BrianWalczak/BKFZ-SubGHz/Other/Mockups/1.png

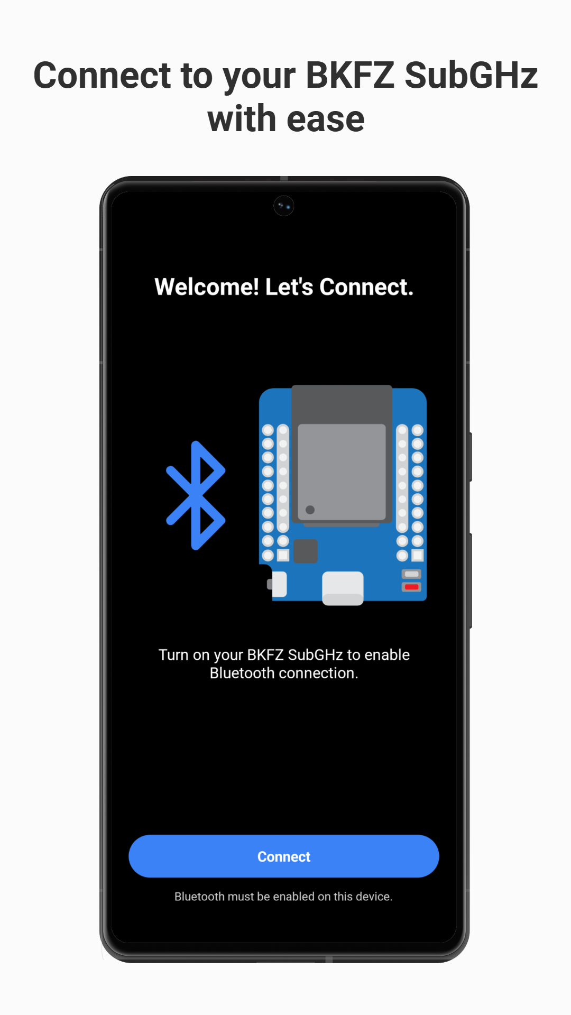
Other/Mockups/1.png
