BrianWalczak/BKFZ-SubGHz/Other/Mockups/2.png

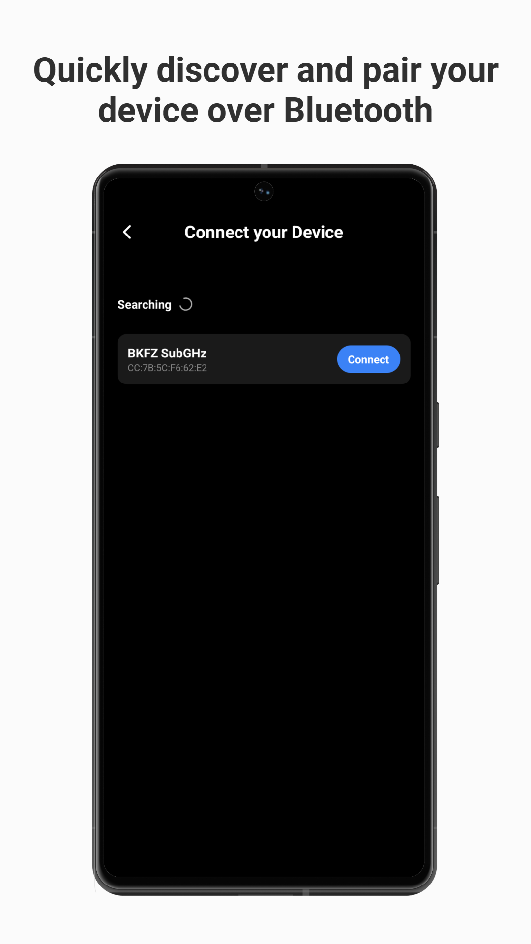
Other/Mockups/2.png
