BrianWalczak/BKFZ-SubGHz/Other/Mockups/3.png

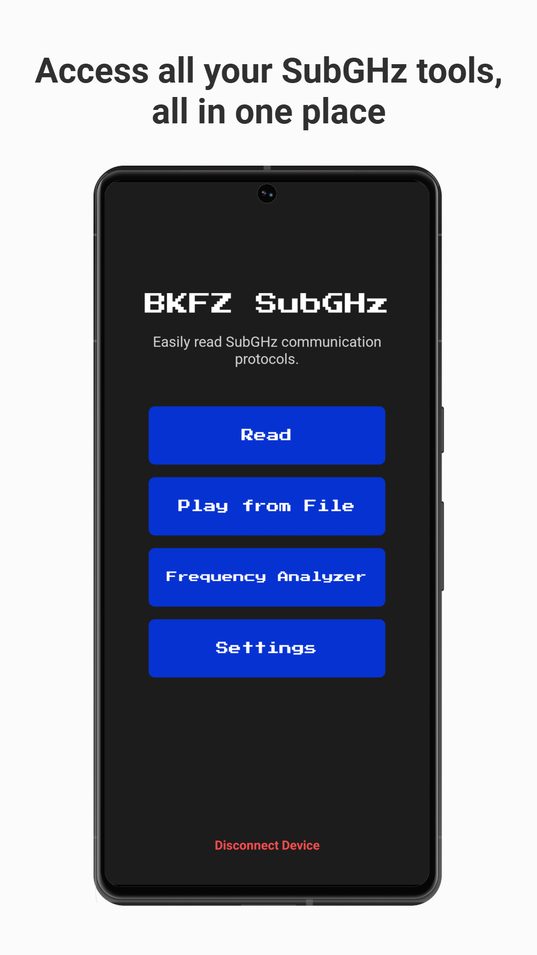
Other/Mockups/3.png
