BrianWalczak/BKFZ-SubGHz/Other/Assembly Photos/Step 1. Soldering to PCB (after).jpeg

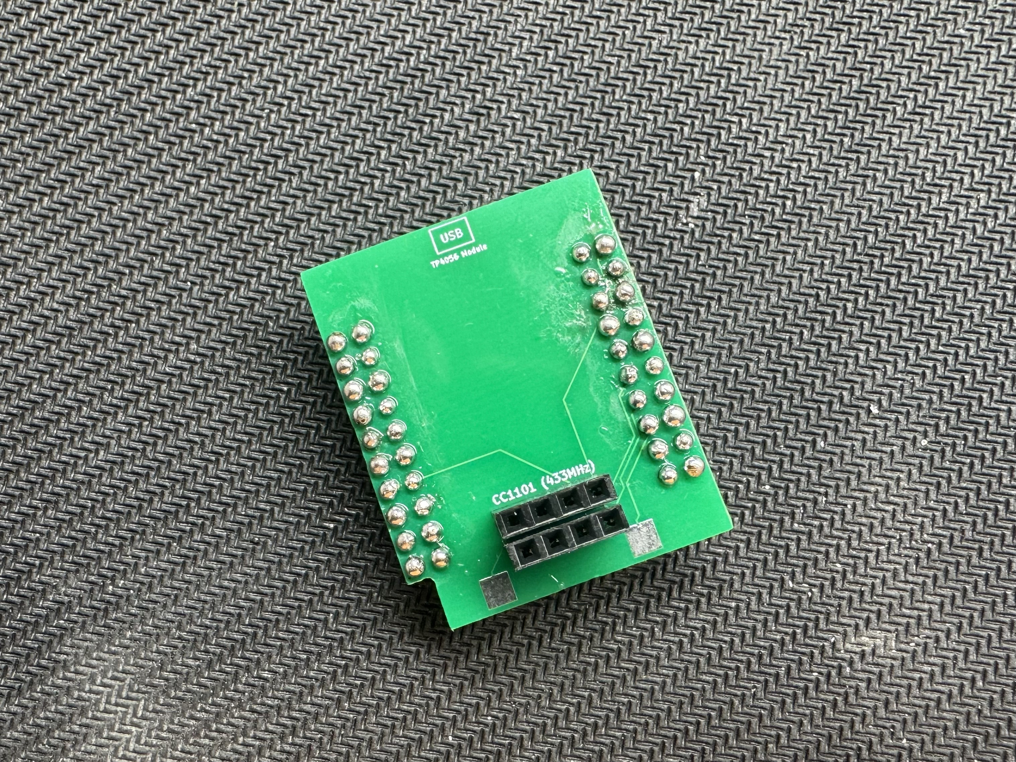
Other/Assembly Photos/Step 1. Soldering to PCB (after).jpeg
