BrianWalczak/BKFZ-SubGHz/Other/Assembly Photos/Step 5. Soldering to Latching Button (#1).jpeg

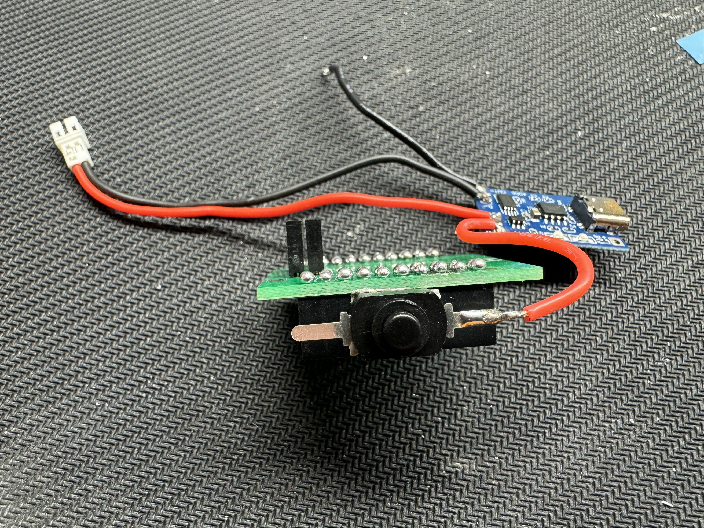
Other/Assembly Photos/Step 5. Soldering to Latching Button (#1).jpeg
