BrianWalczak/BKFZ-SubGHz/Other/Assembly Photos/Step 8. Final Product.jpeg

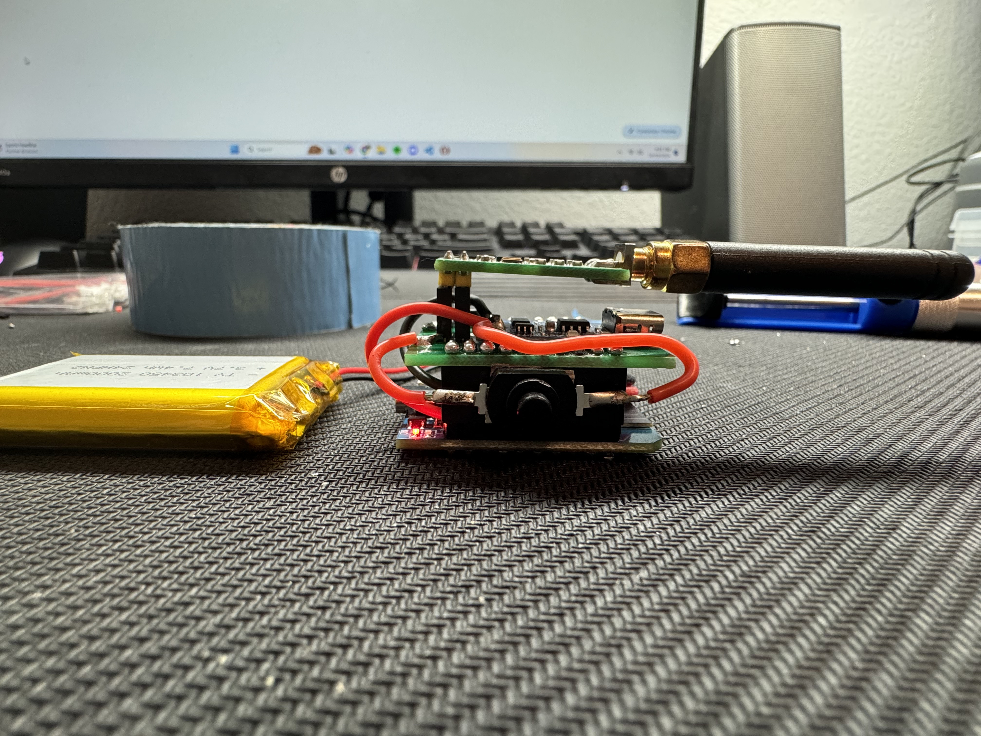
Other/Assembly Photos/Step 8. Final Product.jpeg
