BrianWalczak/BKFZ-SubGHz/Other/Assembly Photos/Step 5. Soldering to Latching Button (#2).jpeg

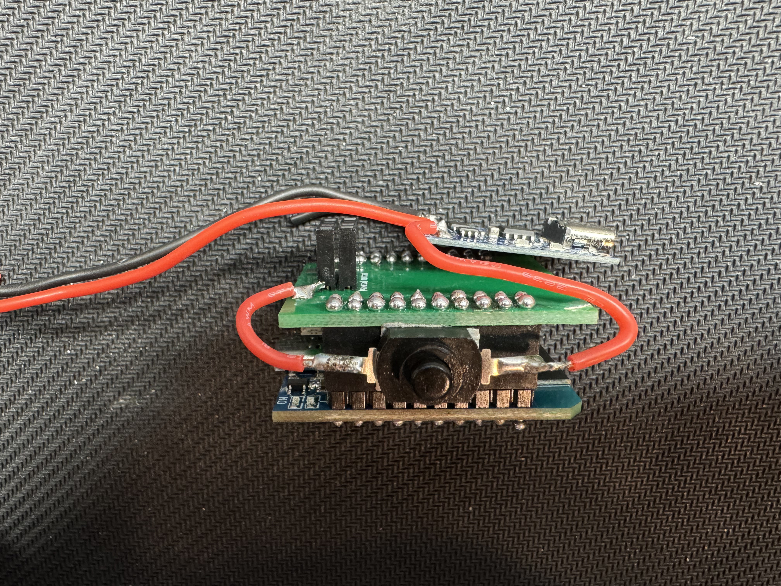
Other/Assembly Photos/Step 5. Soldering to Latching Button (#2).jpeg
